wjcloudy/Stm32-vcu/src/NissLeafMng.cpp

/*
 * This file is part of the ZombieVerter project.
 *
 * Copyright (C) 2021-2023  Tom de Bree <Tom@voltinflux.com>
 *
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
 * You should have received a copy of the GNU General Public License
 * along with this program.  If not, see <http://www.gnu.org/licenses/>.
 */

#include <NissLeafMng.h>

static bool BMSspoof = true;
static bool SendCan = false;
static uint8_t mprun10 = 0;
static uint8_t mprun100 = 0;
static uint8_t OBCpwr = 0;
static uint16_t SleepCount = 0;

CanHardware *can;

void NissLeafMng::SetCanInterface(CanHardware *c) { can = c; }

void NissLeafMng::Task10Ms(int16_t final_torque_request) {
  uint8_t bytes[8];

  int opmode = Param::GetInt(Param::opmode);

  int Dir = Param::GetInt(Param::dir);

  if (SendCan == true) // only send CAN when needed
  {
    mprun10 = (mprun10 + 1) % 4; // mprun10 cycles between 0-1-2-3-0-1...

    /////////////////////////////////////////////////////////////////////////////////////////////////
    // CAN Messaage 0x11A

    // Data taken from a gen1 inFrame where the car is starting to
    // move at about 10% throttle: 4E400055 0000017D

    // All possible gen1 values: 00 01 0D 11 1D 2D 2E 3D 3E 4D 4E
    // MSB nibble: Selected gear (gen1/LeafLogs)
    //   0: some kind of non-gear before driving
    //      0: Park in Gen 2. byte 0 = 0x01 when in park and charging
    //   1: some kind of non-gear after driving
    //   2: R
    //   3: N
    //   4: D
    // LSB nibble: ? (LeafLogs)
    //   0: sometimes at startup, not always; never when the
    //      inverted is powered on (0.06%)
    //   1: this is the usual value (55% of the time in LeafLogs)
    //   D: seems to occur for ~90ms when changing gears (0.2%)
    //   E: this also is a usual value, but never occurs with the
    //      non-gears 0 and 1 (44% of the time in LeafLogs)

    // byte 0 determines motor rotation direction
    if (opmode == MOD_CHARGE) {
      bytes[0] = 0x01; // Car in park when charging
    } else {
      if (Dir == 1) // drive
      {
        bytes[0] = 0x4E;    // Drive
      } else if (Dir == -1) // reverse
      {
        bytes[0] = 0x2E; // Reverse
      } else {
        bytes[0] = 0x01; // Park
      }
    }

    // 0x40 when car is ON, 0x80 when OFF, 0x50 when ECO. Car must be off when
    // charing 0x80
    if (opmode == MOD_CHARGE)
      bytes[1] = 0x80;
    if (opmode != MOD_CHARGE)
      bytes[1] = 0x40;
    // Usually 0x00, sometimes 0x80 (LeafLogs), 0x04 seen by canmsgs
    bytes[2] = 0x00;

    // Weird value at D3:4 that goes along with the counter
    // NOTE: Not actually needed, you can just send constant AA C0
    const static uint8_t weird_d34_values[4][2] = {
        {0xaa, 0xc0},
        {0x55, 0x00},
        {0x55, 0x40},
        {0xaa, 0x80},
    };

    bytes[3] = weird_d34_values[mprun10][0]; // 0xAA;
    bytes[4] = weird_d34_values[mprun10][1]; // 0xC0;
    bytes[5] = 0x00;                         // Always 0x00 (LeafLogs, canmsgs)
    bytes[6] = mprun10;                      // A 2-bit counter
    nissan_crc(bytes, 0x85);

    can->Send(0x11A, (uint32_t *)bytes, 8);

    /////////////////////////////////////////////////////////////////////////////////////////////////
    // CAN Message 0x1D4: Target Motor Torque

    // Data taken from a gen1 inFrame where the car is starting to
    // move at about 10% throttle: F70700E0C74430D4

    // Usually F7, but can have values between 9A...F7 (gen1)
    bytes[0] = 0xF7; // Upper Torque Limit 2.5Nm/bit 617Nm
    // 2016: 6E

    // Usually 07, but can have values between 07...70 (gen1)
    bytes[1] = 0x70; // any val above 0x70 will disable regen on Gen1 Em61 leaf
                     // systems. Later systems allow up to 0xf7

    // 2016: 6E

    // override any torque commands if not in run mode.
    if (opmode != MOD_RUN) {
      final_torque_request = 0;
    }

    // Requested torque (signed 12-bit value + always 0x0 in low nibble)
    if (final_torque_request >= -2048 && final_torque_request <= 2047) {
      bytes[2] = ((final_torque_request < 0) ? 0x80 : 0) |
                 ((final_torque_request >> 4) & 0x7f);
      bytes[3] = (final_torque_request << 4) & 0xf0;
    } else {
      bytes[2] = 0x00;
      bytes[3] = 0x00;
    }

    // MSB nibble: Runs through the sequence 0, 4, 8, C
    // LSB nibble: Precharge report (precedes actual precharge
    //             control)
    //   0: Discharging (5%)
    //   2: Precharge not started (1.4%)
    //   3: Precharging (0.4%)
    //   5: Starting discharge (3x10ms) (2.0%)
    //   7: Precharged (93%)
    if (opmode == MOD_CHARGE || opmode == MOD_RUN) {
      bytes[4] = 0x07; // HV status is ON
    } else if (opmode == MOD_PRECHARGE) {
      bytes[4] = 0x03; // HV status is Precharge
    } else {
      bytes[4] = 0x02; // HV status is OFF
    }
    bytes[4] = bytes[4] | (mprun10 << 6);
    // bytes[4] = 0x02 | (mprun10 << 6);
    // Bit 2 is HV status. 0x00 No HV, 0x01 HV On.

    // MSB nibble:
    //   0: 35-40ms at startup when gear is 0, then at shutdown 40ms
    //      after the car has been shut off (6% total)
    //   4: Otherwise (94%)
    // LSB nibble:
    //   0: ~100ms when changing gear, along with 11A D0 b3:0 value
    //      D (0.3%)
    //   2: Reverse gear related (13%)
    //   4: Forward gear related (21%)
    //   6: Occurs always when gear 11A D0 is 01 or 11 (66%)
    // outFrame.data.bytes[5] = 0x44;
    // outFrame.data.bytes[5] = 0x46;

    // 2016 drive cycle: 06, 46, precharge, 44, drive, 46, discharge, 06
    // 0x46 requires ~25 torque to start
    // outFrame.data.bytes[5] = 0x46;
    // 0x44 requires ~8 torque to start
    bytes[5] = 0x44;
    // bit 6 is Main contactor status. 0x00 Not on, 0x01 on.

    // MSB nibble:
    //   In a drive cycle, this slowly changes between values (gen1):
    //     leaf_on_off.txt:
    //       5 7 3 2 0 1 3 7
    //     leaf_on_rev_off.txt:
    //       5 7 3 2 0 6
    //     leaf_on_Dx3.txt:
    //       5 7 3 2 0 2 3 2 0 2 3 2 0 2 3 7
    //     leaf_on_stat_DRDRDR.txt:
    //       0 1 3 7
    //     leaf_on_Driveincircle_off.txt:
    //       5 3 2 0 8 B 3 2 0 8 A B 3 2 0 8 A B A 8 0 2 3 7
    //     leaf_on_wotind_off.txt:
    //       3 2 0 8 A B 3 7
    //     leaf_on_wotinr_off.txt:
    //       5 7 3 2 0 8 A B 3 7
    //     leaf_ac_charge.txt:
    //       4 6 E 6
    //   Possibly some kind of control flags, try to figure out
    //   using:
    //     grep 000001D4 leaf_on_wotind_off.txt | cut -d' ' -f10 | uniq |
    //     ~/projects/leaf_tools/util/hex_to_ascii_binary.py
    //   2016:
    //     Has different values!
    // LSB nibble:
    //   0: Always (gen1)
    //   1:  (2016)

    // 2016 drive cycle:
    //   E0: to 0.15s
    //   E1: 2 messages
    //   61: to 2.06s (inverter is powered up and precharge
    //                 starts and completes during this)
    //   21: to 13.9s
    //   01: to 17.9s
    //   81: to 19.5s
    //   A1: to 26.8s
    //   21: to 31.0s
    //   01: to 33.9s
    //   81: to 48.8s
    //   A1: to 53.0s
    //   21: to 55.5s
    //   61: 2 messages
    //   60: to 55.9s
    //   E0: to end of capture (discharge starts during this)

    // This value has been chosen at the end of the hardest
    // acceleration in the wide-open-throttle pull, with full-ish
    // torque still being requested, in
    //   LeafLogs/leaf_on_wotind_off.txt
    // outFrame.data.bytes[6] = 0x00;

    // This value has been chosen for being seen most of the time
    // when, and before, applying throttle in the wide-open-throttle
    // pull, in
    //   LeafLogs/leaf_on_wotind_off.txt

    if (opmode != MOD_CHARGE)
      bytes[6] = 0x30; // brake applied heavilly.
    if (opmode == MOD_CHARGE)
      bytes[6] = 0xE0; // charging mode
    // In Gen 2 byte 6 is Charge status.
    // 0x8C Charging interrupted
    // 0xE0 Charging

    // Value chosen from a 2016 log
    // outFrame.data.bytes[6] = 0x61;

    // Value chosen from a 2016 log
    // 2016-24kWh-ev-on-drive-park-off.pcap #12101 / 15.63s
    // outFrame.data.bytes[6] = 0x01;
    // byte 6 brake signal
    nissan_crc(bytes, 0x85);

    can->Send(0x1D4, (uint32_t *)bytes, 8); // send on can1

    /////////////////////////////////////////////////////////////////////////////////////////////////
    // CAN Message 0x1F2: Charge Power and DC/DC Converter Control

    // convert power setpoint to PDM format:
    //    0x70 = 3 amps ish
    //    0x6a = 1.4A
    //    0x66 = 0.5A
    //    0x65 = 0.3A
    //    0x64 = no chg
    //    so 0x64=100. 0xA0=160. so 60 decimal steps. 1 step=100W???
    /////////////////////////////////////////////////////////////////////////////////////////////////////

    // get actual voltage and voltage setpoints
    uint16_t Vbatt = Param::GetInt(Param::udc);
    uint16_t VbattSP = Param::GetInt(Param::Voltspnt);
    uint16_t calcBMSpwr =
        (Vbatt *
         Param::GetInt(
             Param::BMS_ChargeLim)); // BMS charge current limit but needs to be
                                     // power for most AC charger types.

    uint8_t OBCpwrSP =
        (MIN(Param::GetInt(Param::Pwrspnt), calcBMSpwr) / 100) + 0x64;

    if (opmode == MOD_CHARGE &&
        Param::GetInt(Param::Chgctrl) == ChargeControl::Enable) {
      // clamp min and max values
      if (OBCpwrSP > 0xA0) {
        OBCpwrSP = 0xA0;
      }

      // if measured vbatt is less than setpoint got to max power from web ui
      if (Vbatt < VbattSP) {
        OBCpwr = OBCpwrSP;
      }

      // decrement charger power if volt setpoint is reached
      if (Vbatt >= VbattSP) {
        OBCpwr--;
      }

      if (OBCpwrSP < 0x64) {
        OBCpwrSP = 0x64;
      }
    } else {
      // set power to 0 if charge control is set to off or not in charge mode
      OBCpwr = 0x64;
    }

    // Commanded chg power in byte 1 and byte 0 bits 0-1. 10 bit number.
    // byte 1=0x64 and byte 0=0x00 at 0 power.
    // 0x00 chg 0ff dcdc on.
    bytes[0] = 0x30; // msg is muxed but pdm doesn't seem to care.
    bytes[1] = OBCpwr;
    bytes[2] = 0x20; // 0x20=Normal Charge
    bytes[3] = 0xAC;
    bytes[4] = 0x00;
    bytes[5] = 0x3C;
    bytes[6] = mprun10;
    bytes[7] = 0x92; // DCDC Setpoint in PDM

    can->Send(0x1F2, (uint32_t *)bytes, 8);

    if (BMSspoof) {
      /////////////////////////////////////////////////////////////////////////////////////////////////
      // CAN Message 0x1DB

      // We need to send 0x1db here with voltage measured by inverter
      // Zero seems to work also on my gen1
      ////////////////////////////////////////////////////////////////
      // Byte 1 bits 8-10 LB Failsafe Status
      // 0x00 Normal start req. seems to stay on this value most of the time
      // 0x01 Normal stop req
      // 0x02 Charge stop req
      // 0x03 Charge and normal stop req. Other values call for a caution lamp
      // which we don't need bits 11-12 LB relay cut req 0x00 no req
      // 0x01,0x02,0x03 main relay off req
      uint16_t Ibatt = Param::GetInt(Param::idc) * 2;
      Vbatt = Vbatt * 2;
      bytes[0] = Ibatt >> 3;          // MSB current. 11 bit signed MSBit first
      bytes[1] = (Ibatt & 0x07) << 5; // LSB current bits 7-5. Dont need to mess
                                      // with bits 0-4 for now as 0 works.
      bytes[2] = Vbatt >> 2;
      bytes[3] =
          (((Vbatt & 0x07) << 6) | (0x2b)); // 0x2b should give no cut req, main
                                            // rly on permission,normal p limit.
      bytes[4] = 0x40;                      // SOC for dash in Leaf. fixed val.
      bytes[5] = 0x00;
      bytes[6] = mprun10;

      // Extra CRC in byte 7
      nissan_crc(bytes, 0x85);

      can->Send(0x1DB, (uint32_t *)bytes, 8);
    }

    if (BMSspoof) {
      /////////////////////////////////////////////////////////////////////////////////////////////////
      // CAN Message 0x1DC:

      // 0x1dc from lbc. Contains chg power lims and disch power lims.
      // Disch power lim in byte 0 and byte 1 bits 6-7. Just set to max for now.
      // Max charging power in bits 13-20. 10 bit unsigned scale 0.25.Byte 1
      // limit in kw.
      bytes[0] = 0xA0; // 0x6E - 110kw limit 0xA0-160Kw limit
      bytes[1] = 0x0A;
      bytes[2] = 0x05;
      bytes[3] = 0xD5;
      bytes[4] = 0x00; // may not need pairing code crap here...and we don't:)
      bytes[5] = 0x00;
      bytes[6] = mprun10;
      // Extra CRC in byte 7
      nissan_crc(bytes, 0x85);

      can->Send(0x1DC, (uint32_t *)bytes, 8);
    }
  }
}

void NissLeafMng::Task100Ms() {
  uint8_t bytes[8];
  int opmode = Param::GetInt(Param::opmode);

  if (Param::GetInt(Param::BMS_Mode) ==
      4) // Check ran here as this runs on Zombie power on.
  {
    BMSspoof = false;
  } else {
    BMSspoof = true;
  }

  if (SendCan == false) // If not sending CAN check if we need to start
  {
    if (Param::GetInt(Param::CanAct) ==
        1) // External CAN wake trigger (currently only PDM)
    {
      // SendCan = true;
      // SleepCount = 100; // 10s shut down counter reset
    }
    if (opmode == MOD_CHARGE ||
        opmode == MOD_RUN) // If we get put into RUN or Charge mode start CAN
    {
      SendCan = true;
      SleepCount = 15; // 1.5s shut down counter reset
    }
  }

  if (SendCan == true &&
      opmode ==
          MOD_OFF) // stop sending CAN if we are sending CAN and enter OFF mode
  {
    if (SleepCount == 0) {
      SendCan = false;
      Param::SetInt(Param::CanAct, 0); // Reset CAN wake trigger
      // Send CAN sleep command and stop sending CAN
      bytes[0] = 0x00;
      bytes[1] = 0x00;
      bytes[2] = 0x00;
      bytes[3] = 0x00;
      bytes[4] = 0x00;
      bytes[5] = 0x00;
      bytes[6] = 0x00;

      // possible problem here as 0x50B is DLC 7....
      can->Send(0x50B, (uint32_t *)bytes, 7);
    } else {
      SleepCount--;
    }
  }

  if (SendCan == true) // only send CAN when needed
  {
    mprun100 = (mprun100 + 1) % 4; // mprun100 cycles between 0-1-2-3-0-1...

    /////////////////////////////////////////////////////////////////////////////////////////////////
    // CAN Message 0x50B

    // Statistics from 2016 capture:
    //     10 00000000000000
    //     21 000002c0000000
    //    122 000000c0000000
    //    513 000006c0000000

    // Let's just send the most common one all the time
    // FIXME: This is a very sloppy implementation. Thanks. I try:) Dala: This
    // message is not 10ms, it is 100ms
    bytes[0] = 0x00;
    bytes[1] = 0x00;
    bytes[2] = 0x06;
    bytes[3] = 0xc0;
    bytes[4] = 0x00;
    bytes[5] = 0x00;
    bytes[6] = 0x00;

    // possible problem here as 0x50B is DLC 7....
    can->Send(0x50B, (uint32_t *)bytes, 7);

    if (BMSspoof) {
      /////////////////////////////////////////////////////////////////////////////////////////////////
      // CAN Message 0x55B:

      bytes[0] = 0xA4;
      bytes[1] = 0x40;
      bytes[2] = 0xAA;
      bytes[3] = 0x00;
      bytes[4] = 0xDF;
      bytes[5] = 0xC0;
      bytes[6] = ((0x1 << 4) | (mprun100));
      // Extra CRC in byte 7
      nissan_crc(bytes, 0x85);

      can->Send(0x55b, (uint32_t *)bytes, 8);

      /////////////////////////////////////////////////////////////////////////////////////////////////
      // CAN Message 0x59E:

      bytes[0] = 0x00; // Static msg works fine here
      bytes[1] = 0x00; // Batt capacity for chg and qc.
      bytes[2] = 0x0c;
      bytes[3] = 0x76;
      bytes[4] = 0x18;
      bytes[5] = 0x00;
      bytes[6] = 0x00;
      bytes[7] = 0x00;

      can->Send(0x59e, (uint32_t *)bytes, 8);

      /////////////////////////////////////////////////////////////////////////////////////////////////
      // CAN Message 0x5BC:

      // muxed msg with info for gids etc. Will try static for a test.
      bytes[0] = 0x3D; // Static msg works fine here
      bytes[1] = 0x80;
      bytes[2] = 0xF0;
      bytes[3] = 0x64;
      bytes[4] = 0xB0;
      bytes[5] = 0x01;
      bytes[6] = 0x00;
      bytes[7] = 0x32;

      can->Send(0x5bc, (uint32_t *)bytes, 8);
    }
  }
}

void NissLeafMng::nissan_crc(uint8_t *data, uint8_t polynomial) {
  // We want to process 8 bytes with the 8th byte being zero
  data[7] = 0;
  uint8_t crc = 0;
  for (int b = 0; b < 8; b++) {
    for (int i = 7; i >= 0; i--) {
      uint8_t bit = ((data[b] & (1 << i)) > 0) ? 1 : 0;
      if (crc >= 0x80)
        crc = (uint8_t)(((crc << 1) + bit) ^ polynomial);
      else
        crc = (uint8_t)((crc << 1) + bit);
    }
  }
  data[7] = crc;
}
